chazp246/DMP_Jakub_Zahalka/přílohy/Rendery/1.png

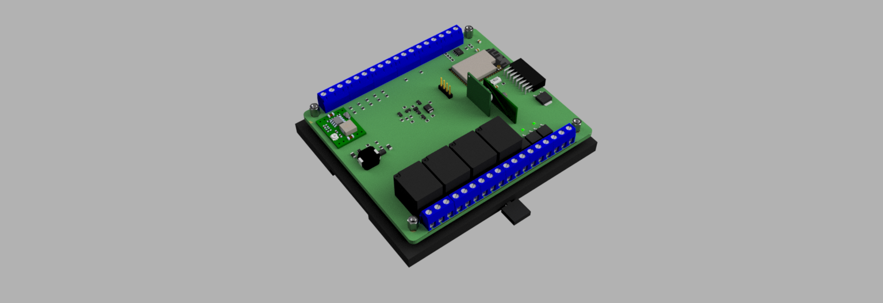
přílohy/Rendery/1.png
