chazp246/DMP_Jakub_Zahalka/přílohy/Rendery/2.png

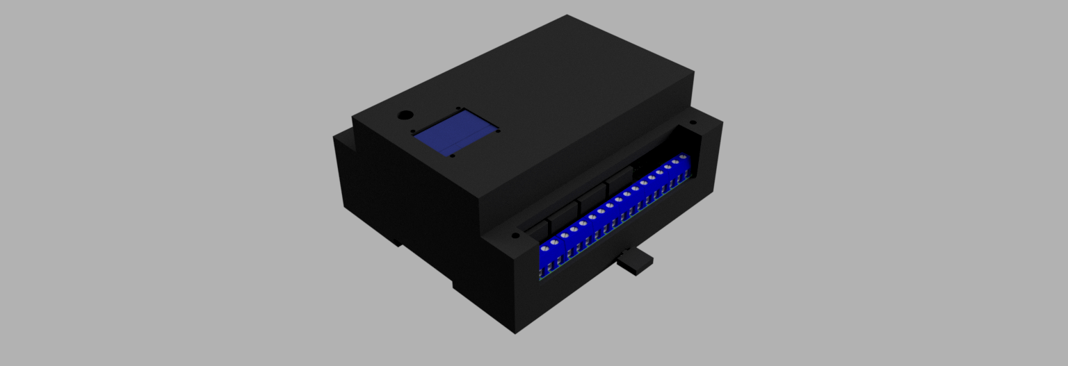
přílohy/Rendery/2.png
