chazp246/DMP_Jakub_Zahalka/přílohy/Rendery/3.png

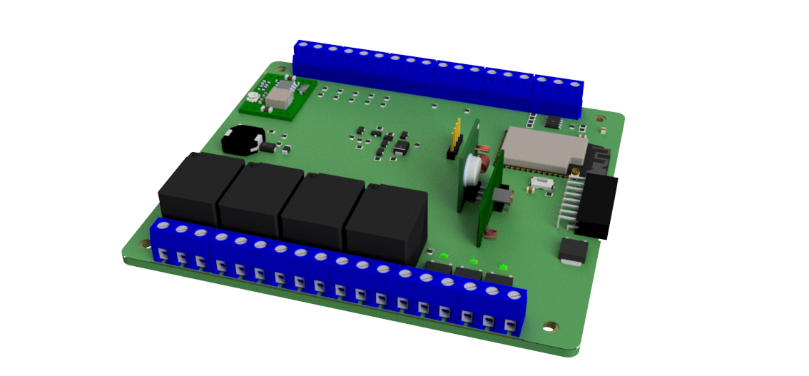
přílohy/Rendery/3.png
